lizcorson/rhtlogger/circuitdiagram/rhtlogger_bb.png

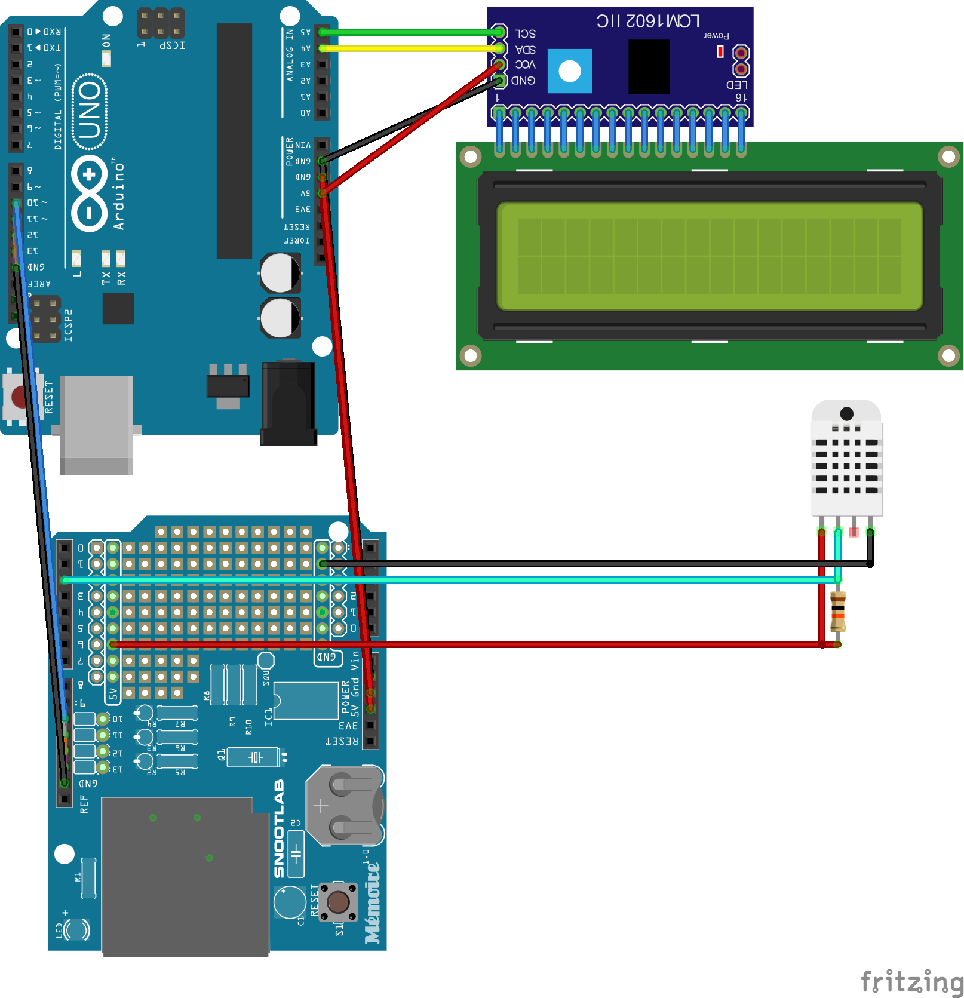
circuitdiagram/rhtlogger_bb.png
